adamryman/spinbit/arduino/BluetoothSerial/BluetoothSerial.ino

/*
  Example Bluetooth Serial Passthrough Sketch
 by: Jim Lindblom
 SparkFun Electronics
 date: February 26, 2013
 license: Public domain

 This example sketch converts an RN-42 bluetooth module to
 communicate at 9600 bps (from 115200), and passes any serial
 data between Serial Monitor and bluetooth module.
 */
 
#include <SoftwareSerial.h>  

int bluetoothTx = 2;  // TX - TX
int bluetoothRx = 3;  // RX - RX

SoftwareSerial bluetooth(bluetoothTx, bluetoothRx);

void setup()
{
  Serial.begin(9600);  // Begin the serial monitor at 9600bps

  bluetooth.begin(9600);  // The Bluetooth Mate defaults to 115200bps
  delay(100);  // Short delay, wait for the Mate to send back CMD
}

void loop()
{
  if(bluetooth.available())  // If the bluetooth sent any characters
  {
    // Send any characters the bluetooth prints to the serial monitor
    Serial.print((char)bluetooth.read());  
  }
  if(Serial.available())  // If stuff was typed in the serial monitor
  {
    // Send any characters the Serial monitor prints to the bluetooth
    bluetooth.print((char)Serial.read());
  }
  // and loop forever and ever!
}
